Robotics-DAI-FMFI-UK/nico-emotions/Python scripts/position_generator/faces/closed.jpg

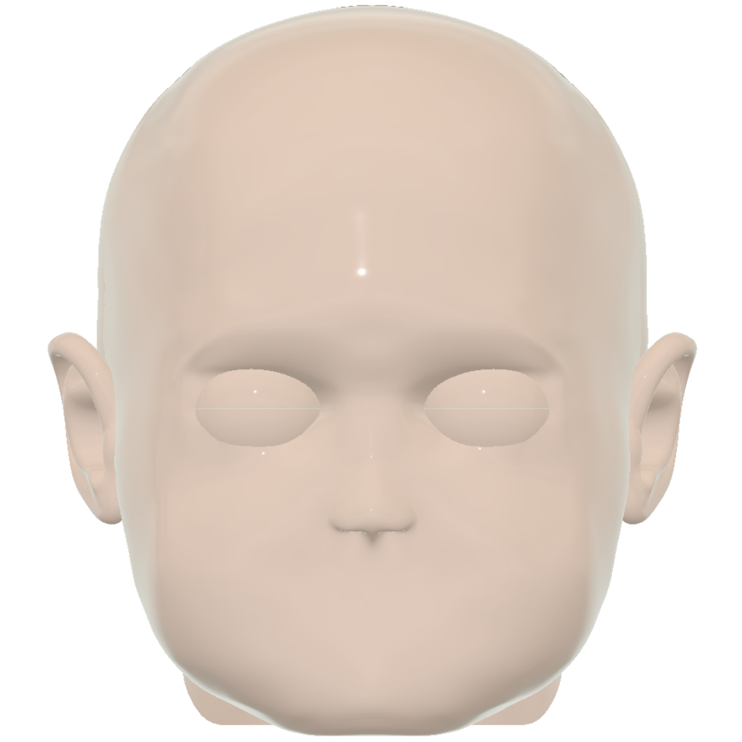
Python scripts/position_generator/faces/closed.jpg
