Robotics-DAI-FMFI-UK/nico-emotions/3D objects/Eyes/eyeball-hinge-v3.stl

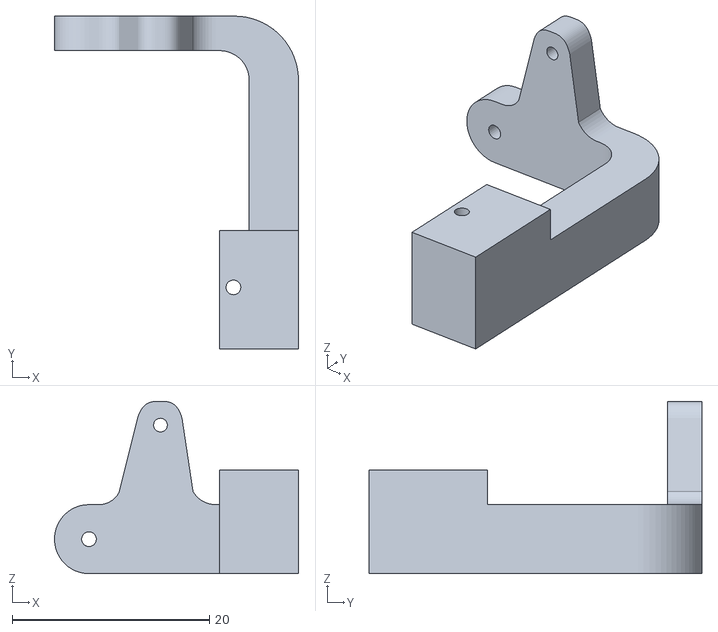
[picture p16: CAD file, 2025-06-24]
3D objects/Eyes/eyeball-hinge-v3.stl
24.7 x 33.8 x 17.5
