Robotics-DAI-FMFI-UK/nico-emotions/3D objects/Head/front.obj

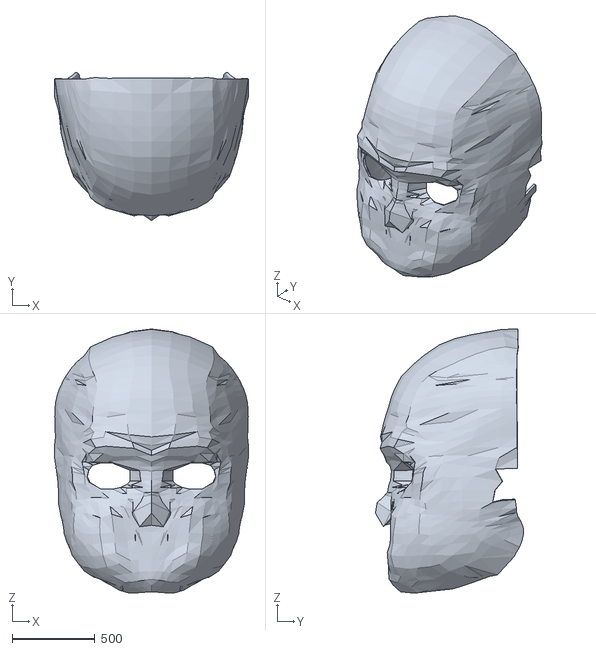
[picture p17: CAD file, 2025-06-24]
3D objects/Head/front.obj
1173.3 x 895.3 x 1594.7
