Robotics-DAI-FMFI-UK/nico-emotions/3D objects/Eyes/lid-low.stl

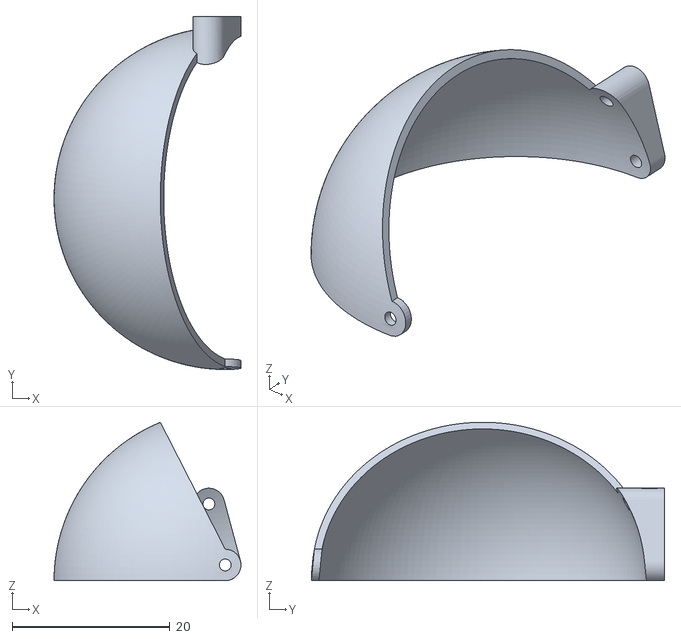
[picture p18: CAD file, 2025-06-24]
3D objects/Eyes/lid-low.stl
23.7 x 44.8 x 20.1
