Robotics-DAI-FMFI-UK/nico-emotions/3D objects/Head/mouth_lower.stl

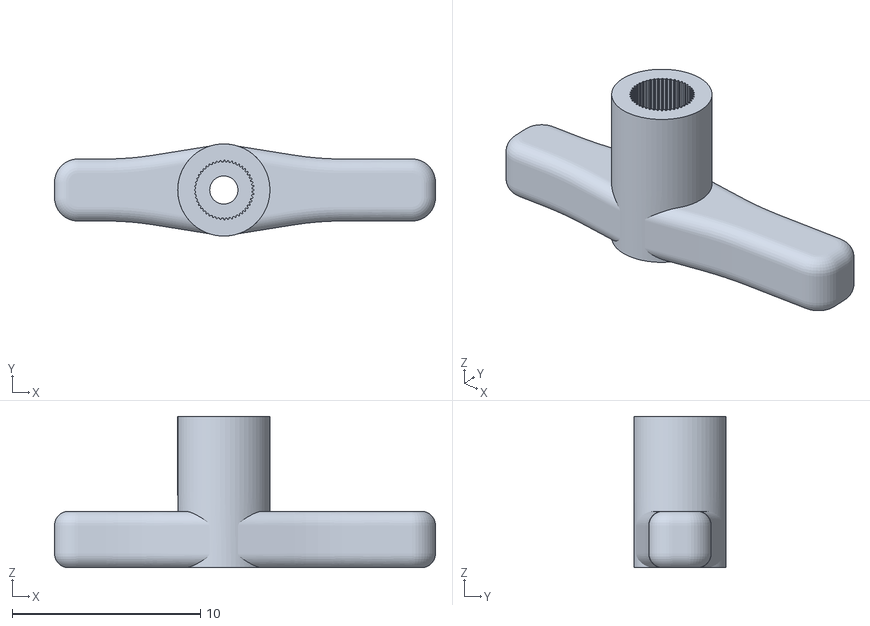
[picture p19: CAD file, 2025-06-24]
3D objects/Head/mouth_lower.stl
20.2 x 4.90 x 8.05
