Robotics-DAI-FMFI-UK/nico-emotions/3D objects/Eyes/lid-slider.stl

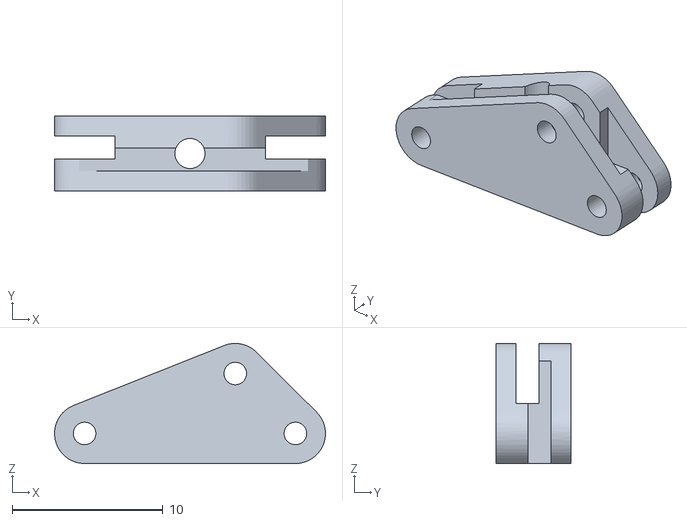
[picture p20: CAD file, 2025-06-24]
3D objects/Eyes/lid-slider.stl
18.0 x 5.00 x 7.98
