Robotics-DAI-FMFI-UK/nico-emotions/3D objects/Head/eyebrow.stl

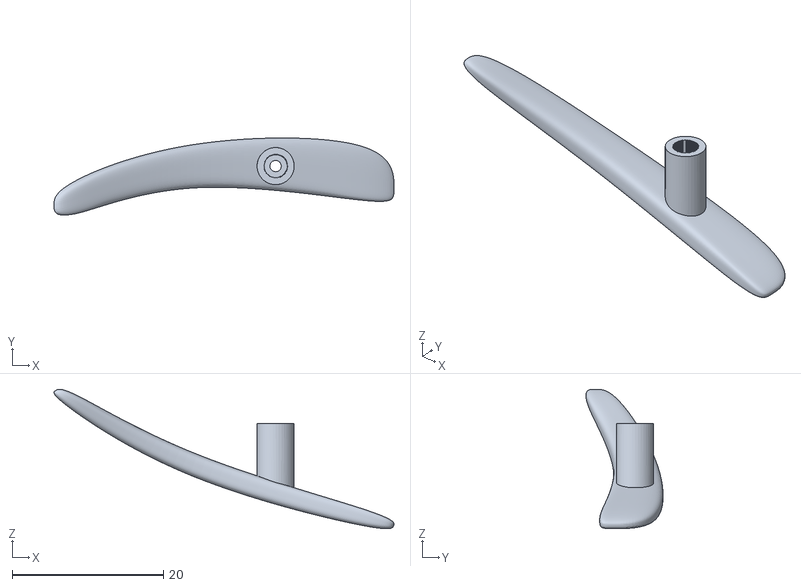
[picture p21: CAD file, 2025-06-24]
3D objects/Head/eyebrow.stl
44.9 x 10.2 x 18.4
