Robotics-DAI-FMFI-UK/nico-emotions/3D objects/Eyes/iris2.stl

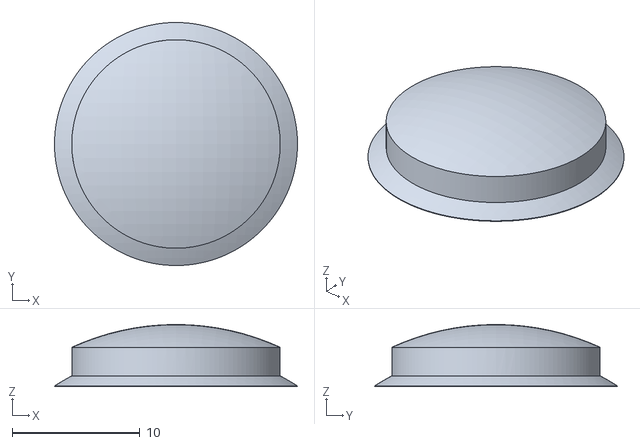
[picture p22: CAD file, 2025-06-24]
3D objects/Eyes/iris2.stl
19.0 x 19.0 x 4.85
