Robotics-DAI-FMFI-UK/nico-emotions/3D objects/Eyes/hingeframe.stl

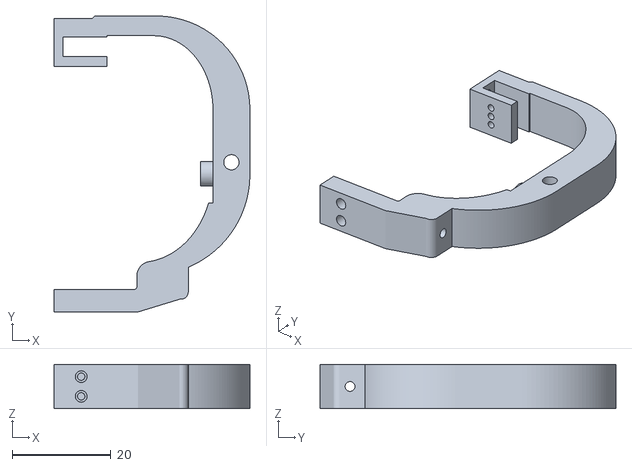
[picture p23: CAD file, 2025-06-24]
3D objects/Eyes/hingeframe.stl
39.8 x 60.1 x 9.00
