Robotics-DAI-FMFI-UK/nico-emotions/Python scripts/Controllers/config.py

# Konfiguracia pre preferovane porty
PREFFERED_PORT = "COM14"
LAST_CONNECTED_PORT = "COM21"

# Nastavenia kamery
CAMERA_DIMENSIONS = (1280, 720)  # (width, height)
MAXIMUM_STORED_DEPTH_DISTANCES = 10 
RGB_CAMERA_FPS = 30
DEPTH_CAMERA_FPS = 30
DEPTH_CAMERA_KERNEL_SIZE = 10

# Globalne nastavenia
MM_TO_PIXEL = 3.7795275591
DIFFERENCE_EYES = (-34, 34) # (Left, Right) in mm
DIFFERENCE_HEAD = (40, -113, 5) # (dx, dy, dz) in mm
EYE_LIMIT_HORIZONTAL = 30
EYE_LIMIT_VERTICAL = 17
EYE_LIMIT_LID = 50
